FASTSHIFT/WatchX/WatchX/ArduinoAPI/HardwareSerial.h

/*
 * MIT License
 * Copyright (c) 2019 _VIFEXTech
 * 
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
 * THE SOFTWARE IS PROVIDED "AS IS", WITHOUT WARRANTY OF ANY KIND, EXPRESS OR
 * IMPLIED, INCLUDING BUT NOT LIMITED TO THE WARRANTIES OF MERCHANTABILITY,
 * FITNESS FOR A PARTICULAR PURPOSE AND NONINFRINGEMENT. IN NO EVENT SHALL THE
 * AUTHORS OR COPYRIGHT HOLDERS BE LIABLE FOR ANY CLAIM, DAMAGES OR OTHER
 * LIABILITY, WHETHER IN AN ACTION OF CONTRACT, TORT OR OTHERWISE, ARISING FROM,
 * OUT OF OR IN CONNECTION WITH THE SOFTWARE OR THE USE OR OTHER DEALINGS IN THE
 * SOFTWARE.
 */
#ifndef __HardwareSerial_h
#define __HardwareSerial_h

#include "Arduino.h"
#include "Print.h"
#include "Stream.h"

#define SERIAL_RX_BUFFER_SIZE 128
#define SERIAL_Config_Default SERIAL_8N1
#define USART_PreemptionPriority_Default 1
#define USART_SubPriority_Default 3

#define USART_GetWordLength(SERIAL_x)    ((uint16_t)(SERIAL_x&0xF000))
#define USART_GetParity(SERIAL_x)        ((uint16_t)(SERIAL_x&0x0F00))
#define USART_GetStopBits(SERIAL_x)      ((uint16_t)((SERIAL_x&0x00F0)<<8))

typedef enum
{
    SERIAL_8N1 = USART_WordLength_8b | USART_Parity_No | (USART_StopBits_1 >> 8),
    SERIAL_8N2 = USART_WordLength_8b | USART_Parity_No | (USART_StopBits_2 >> 8),
    SERIAL_8E1 = USART_WordLength_8b | USART_Parity_Even | (USART_StopBits_1 >> 8),
    SERIAL_8E2 = USART_WordLength_8b | USART_Parity_Even | (USART_StopBits_2 >> 8),
    SERIAL_8O1 = USART_WordLength_8b | USART_Parity_Odd | (USART_StopBits_1 >> 8),
    SERIAL_8O2 = USART_WordLength_8b | USART_Parity_Odd | (USART_StopBits_2 >> 8),
    SERIAL_8N0_5 = USART_WordLength_8b | USART_Parity_No | (USART_StopBits_0_5 >> 8),
    SERIAL_8N1_5 = USART_WordLength_8b | USART_Parity_No | (USART_StopBits_1_5 >> 8),
    SERIAL_8E0_5 = USART_WordLength_8b | USART_Parity_Even | (USART_StopBits_0_5 >> 8),
    SERIAL_8E1_5 = USART_WordLength_8b | USART_Parity_Even | (USART_StopBits_1_5 >> 8),
    SERIAL_8O0_5 = USART_WordLength_8b | USART_Parity_Odd | (USART_StopBits_0_5 >> 8),
    SERIAL_8O1_5 = USART_WordLength_8b | USART_Parity_Odd | (USART_StopBits_1_5 >> 8),

    SERIAL_9N1 = USART_WordLength_9b | USART_Parity_No | (USART_StopBits_1 >> 8),
    SERIAL_9N2 = USART_WordLength_9b | USART_Parity_No | (USART_StopBits_2 >> 8),
    SERIAL_9E1 = USART_WordLength_9b | USART_Parity_Even | (USART_StopBits_1 >> 8),
    SERIAL_9E2 = USART_WordLength_9b | USART_Parity_Even | (USART_StopBits_2 >> 8),
    SERIAL_9O1 = USART_WordLength_9b | USART_Parity_Odd | (USART_StopBits_1 >> 8),
    SERIAL_9O2 = USART_WordLength_9b | USART_Parity_Odd | (USART_StopBits_2 >> 8),
    SERIAL_9N0_5 = USART_WordLength_9b | USART_Parity_No | (USART_StopBits_0_5 >> 8),
    SERIAL_9N1_5 = USART_WordLength_9b | USART_Parity_No | (USART_StopBits_1_5 >> 8),
    SERIAL_9E0_5 = USART_WordLength_9b | USART_Parity_Even | (USART_StopBits_0_5 >> 8),
    SERIAL_9E1_5 = USART_WordLength_9b | USART_Parity_Even | (USART_StopBits_1_5 >> 8),
    SERIAL_9O0_5 = USART_WordLength_9b | USART_Parity_Odd | (USART_StopBits_0_5 >> 8),
    SERIAL_9O1_5 = USART_WordLength_9b | USART_Parity_Odd | (USART_StopBits_1_5 >> 8),
} SERIAL_Config;

class HardwareSerial : public Stream
{
    typedef uint16_t rx_buffer_index_t;
    typedef void(*USART_CallbackFunction_t)(void);
public:
    HardwareSerial(USART_TypeDef *USARTx);
    void IRQHandler();
    void begin(uint32_t BaudRate);
    void begin(uint32_t BaudRate, SERIAL_Config Config);
    void begin(uint32_t BaudRate, SERIAL_Config Config, uint8_t PreemptionPriority, uint8_t SubPriority);
    void end(void);
    void attachInterrupt(USART_CallbackFunction_t Function);
    virtual int available(void);
    virtual int peek(void);
    virtual int read(void);
    virtual void flush(void);

    virtual size_t write(uint8_t n);
    inline size_t write(unsigned long n)
    {
        return write((uint8_t)n);
    }
    inline size_t write(long n)
    {
        return write((uint8_t)n);
    }
    inline size_t write(unsigned int n)
    {
        return write((uint8_t)n);
    }
    inline size_t write(int n)
    {
        return write((uint8_t)n);
    }
    using Print::write; // pull in write(str) and write(buf, size) from Print
    operator bool()
    {
        return true;
    }

private:
    USART_TypeDef *USARTx;
    USART_CallbackFunction_t USART_Function;
    volatile uint16_t _rx_buffer_head;
    volatile uint16_t _rx_buffer_tail;
    uint8_t _rx_buffer[SERIAL_RX_BUFFER_SIZE];
};

extern HardwareSerial Serial;
extern HardwareSerial Serial2;
extern HardwareSerial Serial3;

#endif
