FASTSHIFT/WatchX/WatchX/ArduinoAPI/Tone.cpp

/*
 * MIT License
 * Copyright (c) 2019 _VIFEXTech
 * 
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
 * THE SOFTWARE IS PROVIDED "AS IS", WITHOUT WARRANTY OF ANY KIND, EXPRESS OR
 * IMPLIED, INCLUDING BUT NOT LIMITED TO THE WARRANTIES OF MERCHANTABILITY,
 * FITNESS FOR A PARTICULAR PURPOSE AND NONINFRINGEMENT. IN NO EVENT SHALL THE
 * AUTHORS OR COPYRIGHT HOLDERS BE LIABLE FOR ANY CLAIM, DAMAGES OR OTHER
 * LIABILITY, WHETHER IN AN ACTION OF CONTRACT, TORT OR OTHERWISE, ARISING FROM,
 * OUT OF OR IN CONNECTION WITH THE SOFTWARE OR THE USE OR OTHER DEALINGS IN THE
 * SOFTWARE.
 */
#include "Tone.h"

static TIM_TypeDef *ToneTimer_Last = 0, *ToneTimer = ToneTimer_Default;
static uint8_t tone_State = Off;
static uint8_t tone_Pin;
static uint32_t tone_StopTimePoint;

/**
  * @brief  tone中断入口，被定时中断调用
  * @param  无
  * @retval 无
  */
static void tone_TimerHandler()
{
    togglePin(tone_Pin);
    if(millis() > tone_StopTimePoint && !tone_State)
    {
        noTone(tone_Pin);
    }
}

/**
  * @brief  改变tone所使用的定时器
  * @param  TIMx: 定时器地址
  * @retval 无
  */
void toneSetTimer(TIM_TypeDef* TIMx)
{
    if(IS_TIM_ALL_PERIPH(TIMx))
        ToneTimer = TIMx;
}

/**
  * @brief  在Pin上生成指定频率 (50%占空比的方波)
  * @param  pin: 产生音调的 Pin
  * @param  freq: 频率(Hz)
  * @param  Time_ms: 音调的持续时间 (以毫秒为单位)
  * @retval 无
  */
void tone(uint8_t Pin, uint32_t freq, uint32_t Time_ms)
{
    if(freq == 0 || Time_ms == 0 || freq > 500000)
    {
        noTone(Pin);
        return;
    }
    tone(Pin, freq);
    tone_StopTimePoint = millis() + Time_ms;
    tone_State = Off;
}

/**
  * @brief  在Pin上生成指定频率 (50%占空比的方波)
  * @param  pin: 产生音调的引脚编号
  * @param  freq: 频率(Hz)
  * @retval 无
  */
void tone(uint8_t Pin, uint32_t freq)
{
    if(freq == 0 || freq > 500000)
    {
        noTone(Pin);
        return;
    }
    tone_Pin = Pin;
    tone_State = On;

    if(ToneTimer != ToneTimer_Last)
    {
        Timer_SetInterruptBase(
            ToneTimer, 
            0xFF, 0xFF,
            tone_TimerHandler, 
            0, 0
        );
        Timer_SetInterruptTimeUpdate(ToneTimer, (500000.0f / freq));
        TIM_Cmd(ToneTimer, ENABLE);
        ToneTimer_Last = ToneTimer;
    }
    else
    {
        Timer_SetInterruptTimeUpdate(ToneTimer, (500000.0f / freq));
        TIM_Cmd(ToneTimer, ENABLE);
    }
}

/**
  * @brief  关闭声音
  * @param  Pin: 产生音调的引脚编号
  * @retval 无
  */
void noTone(uint8_t Pin)
{
    TIM_Cmd(ToneTimer, DISABLE);
    digitalWrite(Pin, LOW);
    tone_State = Off;
}

/**
* @brief  在Pin上生成指定频率 (50%占空比的方波，阻塞式不占用定时器)
  * @param  pin: 产生音调的引脚编号
  * @param  freq: 频率(Hz)
  * @param  Time_ms: 音调的持续时间 (以毫秒为单位)
  * @retval 无
  */
void toneBlock(uint8_t Pin, uint32_t freq, uint32_t Time_ms)
{
    uint32_t TimePoint = millis() + Time_ms;
    uint32_t dlyus = 500000 / freq;
    if(freq == 0)return;
    do
    {
        digitalWrite_HIGH(Pin);
        delayMicroseconds(dlyus);
        digitalWrite_LOW(Pin);
        delayMicroseconds(dlyus);
    }
    while(millis() < TimePoint);
    digitalWrite_LOW(Pin);
}

/**
  * @brief  在Pin上生成指定频率和音量 (50%占空比的方波，阻塞式不占用定时器)
  * @param  pin: 产生音调的引脚编号
  * @param  freq: 频率(Hz)
  * @param  Time_ms: 音调的持续时间 (以毫秒为单位)
  * @param  vol: 音量(0-100)
  * @retval 无
  */
void toneBlock_Volumn(uint8_t Pin, uint32_t freq, uint32_t Time_ms, uint32_t vol)
{
    uint32_t TimePoint = millis() + Time_ms;
    uint32_t dlyus = 500000 / freq;
    uint32_t dlHigh = dlyus * vol / 100;
    uint32_t dlLow = 2 * dlyus - dlHigh;
    if(freq == 0)return;
    do
    {
        digitalWrite_HIGH(Pin);
        delayMicroseconds(dlHigh);
        digitalWrite_LOW(Pin);
        delayMicroseconds(dlLow);
    }
    while(millis() < TimePoint);
    digitalWrite_LOW(Pin);
}

/**
  * @brief  在Pin上生成指定频率和音量 (50%占空比的方波，阻塞式不占用定时器)
  * @param  pin: 产生音调的引脚编号
  * @param  freq: 频率(Hz)
  * @param  Time_us: 音调的持续时间 (以微秒为单位)
  * @param  vol: 音量(0-100)
  * @retval 无
  */
void toneBlock_Volumn_us(uint8_t Pin, uint32_t freq, uint32_t Time_us, uint32_t vol)
{
    uint32_t TimePoint = micros() + Time_us;
    uint32_t dlyus = 500000 / freq;
    uint32_t dlHigh = dlyus * vol / 100;
    uint32_t dlLow = 2 * dlyus - dlHigh;
    if(freq == 0)return;
    do
    {
        digitalWrite_HIGH(Pin);
        delayMicroseconds(dlHigh);
        digitalWrite_LOW(Pin);
        delayMicroseconds(dlLow);
    }
    while(micros() < TimePoint);
    digitalWrite_LOW(Pin);
}
