FASTSHIFT/WatchX/WatchX/WatchX/Game/Arduboy2/Arduboy2Audio.cpp

/**
 * @file Arduboy2Audio.cpp
 * \brief
 * The Arduboy2Audio class for speaker and sound control.
 */

#include "Arduboy2.h"
#include "Arduboy2Audio.h"

bool Arduboy2Audio::audio_enabled = false;

void Arduboy2Audio::on()
{
  // fire up audio pins by seting them as outputs

  audio_enabled = true;
}

void Arduboy2Audio::off()
{
  audio_enabled = false;
  // shut off audio pins by setting them as inputs
}

void Arduboy2Audio::toggle()
{
  if (audio_enabled)
    off();
  else
    on();
}

void Arduboy2Audio::saveOnOff()
{
  //EEPROM.update(EEPROM_AUDIO_ON_OFF, audio_enabled);
}

void Arduboy2Audio::begin()
{
  if (1/*EEPROM.read(EEPROM_AUDIO_ON_OFF)*/)
    on();
  else
    off();
}

bool Arduboy2Audio::enabled()
{
  return audio_enabled;
}
