FASTSHIFT/WatchX/WatchX/WatchX/Game/chribocchi/common.h

#ifndef COMMON_H
#define COMMON_H

#include "MyArduboy.h"

/*  Defines  */

//#define DEBUG
#define APP_TITLE       "CHRI-BOCCHI CAT"
#define APP_INFO        "OBN-Y03 VER 0.03"
#define APP_RELEASED    "DECEMBER 2017"

/*  Typedefs  */

typedef unsigned char   uchar;
typedef unsigned int    uint;

/*  Global Functions  */

void initLogo(void);
bool updateLogo(void);
void drawLogo(void);

void initTitle(void);
bool updateTitle(void);
void drawTitle(void);
uint8_t setLastScore(int score, uint32_t time);

void initGame(void);
bool updateGame(void);
void drawGame(void);

/*  Global Variables  */

extern MyArduboy arduboy;

/*  For Debugging  */

#ifdef DEBUG
extern bool             dbgPrintEnabled;
extern char             dbgRecvChar;
#define dprint(...)     (!dbgPrintEnabled || Serial.print(__VA_ARGS__))
#define dprintln(...)   (!dbgPrintEnabled || Serial.println(__VA_ARGS__))
#else
#define dprint(...)
#define dprintln(...)
#endif

#endif // COMMON_H
